theoanu/openDrivePlatform/hardware/lowVoltageDrive/lowVoltageDrive.sch

## KiCad design hardware/lowVoltageDrive/lowVoltageDrive.sch (2013-01-29)

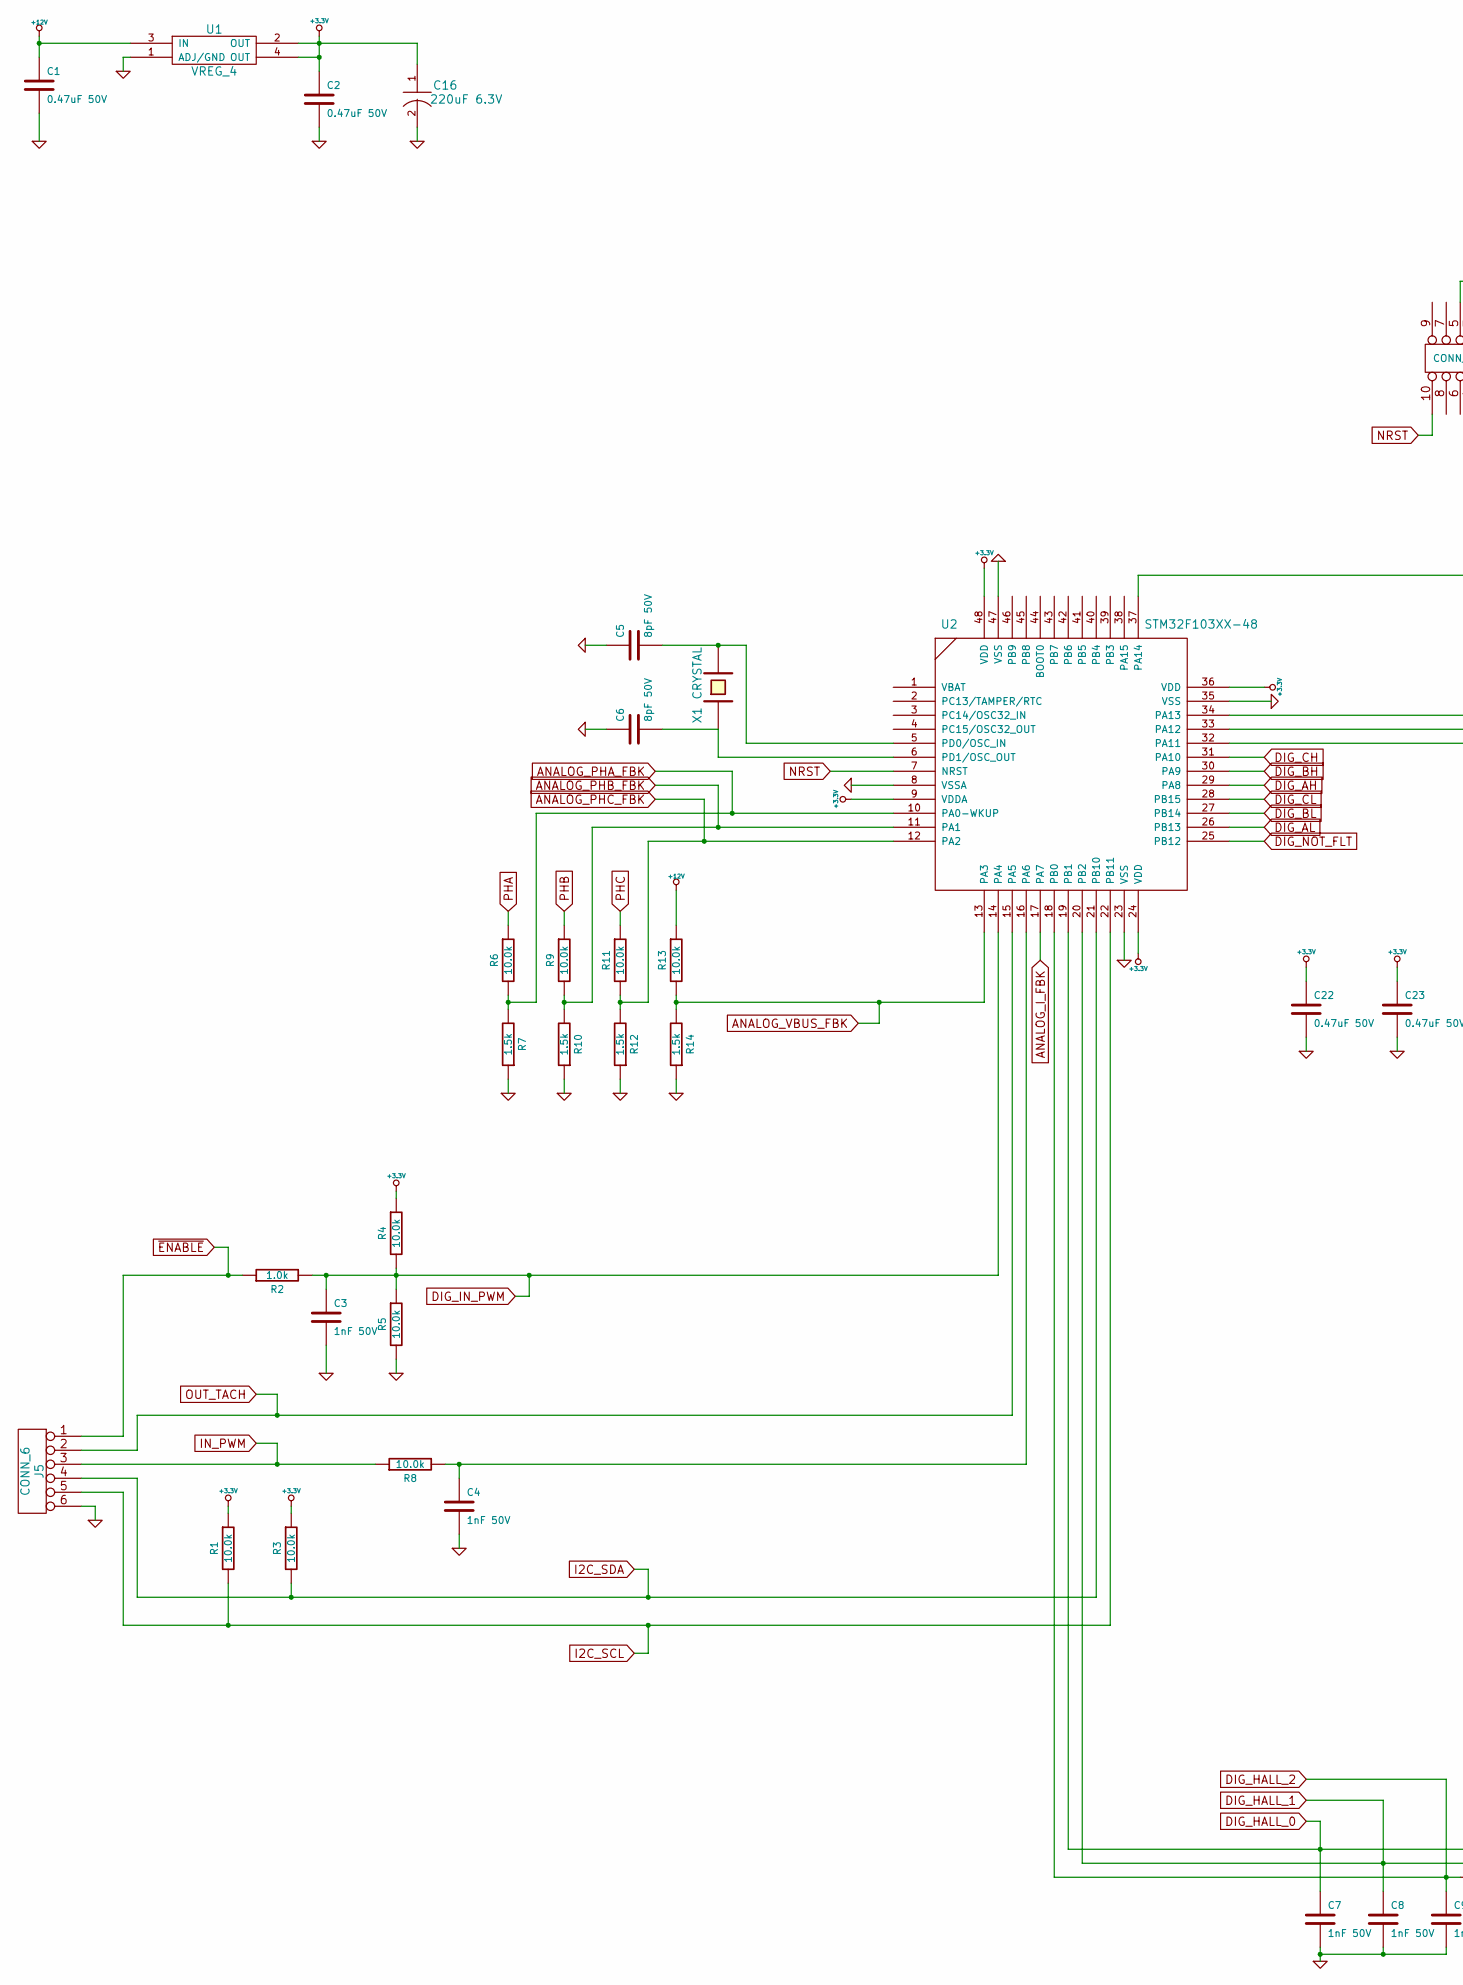
[picture p2: schematic lowVoltageDrive.sch, part in row 1, column 1]

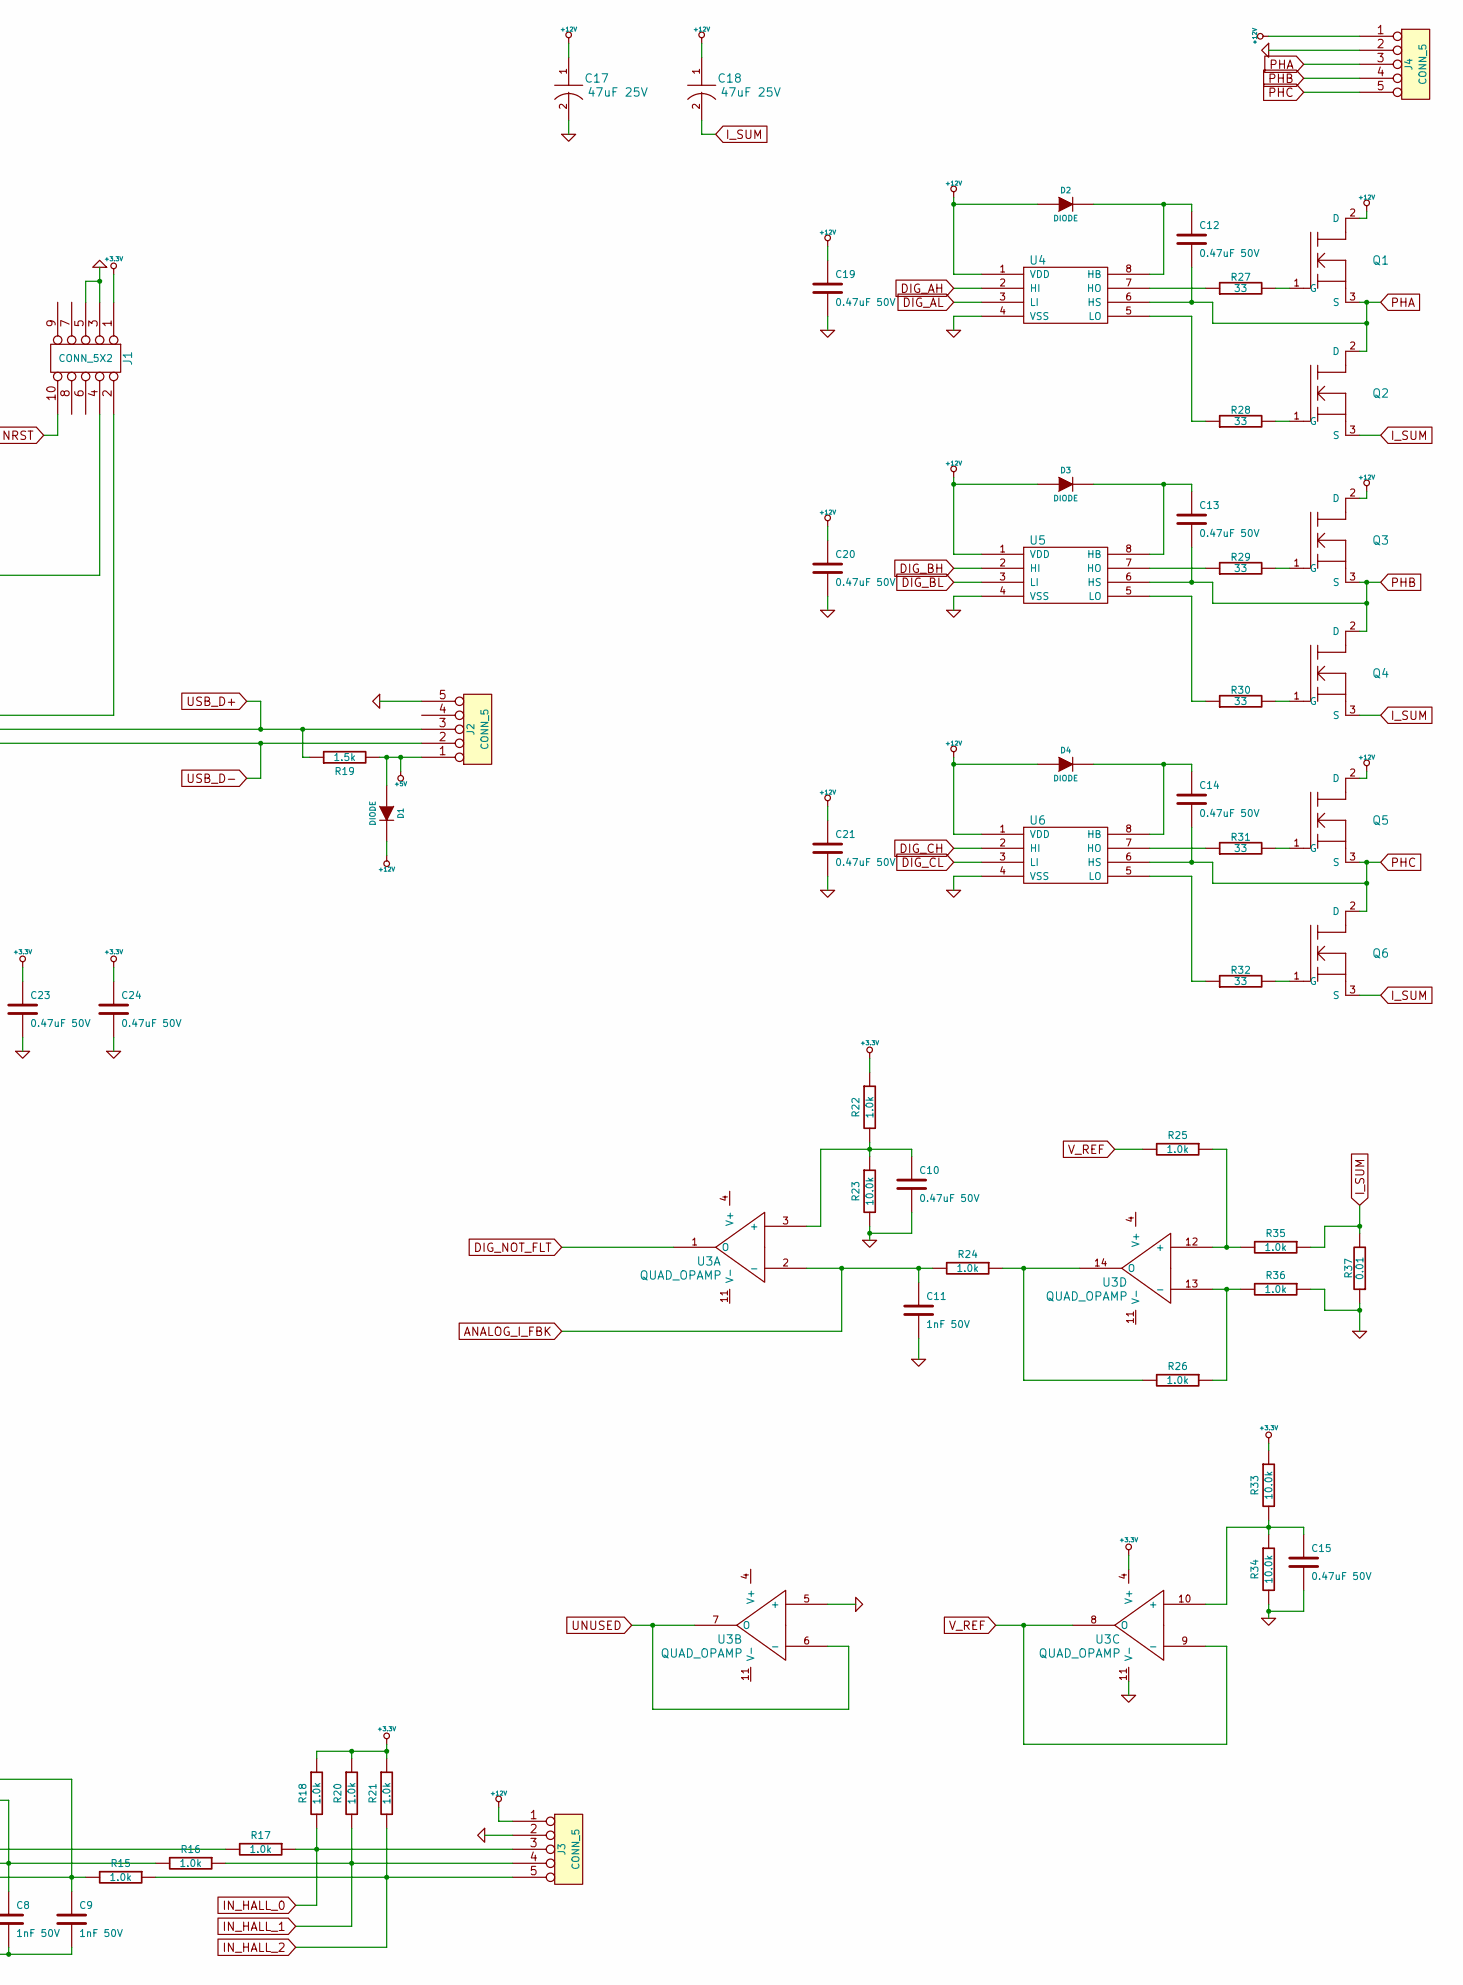
[picture p3: schematic lowVoltageDrive.sch, part in row 1, column 2]

Parts:
C1, C2, C10, C12, C13, C14, C15, C19, C20, C21, C22, C23, C24: 0.47uF 50V; SM0603; Man. Part Number UMK107B7474KA-TR
C3, C4, C7, C8, C9, C11: 1nF 50V; SM0603; Man. Part Number GRM188R71H102KA01D
C5, C6: 8pF 50V; SM0603; Man. Part Number C1608C0G1H080C
C16: 220uF 6.3V; SM_CAP_ALUM_6D3; Man. Part Number EEE-0JA221WP
C17, C18: 47uF 25V; SM_CAP_ALUM_6D3; Man. Part Number EEV476M025A9GAA
D1, D2, D3, D4: DIODE; SOD323; Man. Part Number 1N4148WX-TP
J1: CONN_5X2; CONN10_5X2_0.050
J2: CONN_5; USB_MICRO_AB
J3: CONN_5; CONN5_5-1775444-5; Man. Part Number 5-1775444-5
J4: CONN_5; CONN5_OSTTC050162; Man. Part Number OSTTC050162
J5: CONN_6; CONN6_5-1775444-6; Man. Part Number 5-1775444-6
Q1, Q2, Q3, Q4, Q5, Q6: MOSFET_N_TO220; TO-220-3_tripod; Man. Part Number AOTF240L
R1, R3, R4, R5, R6, R8, R9, R11, R13, R23, R33, R34: 10.0k; SM0603; Man. Part Number RC0603FR-0710KL
R2, R15, R16, R17, R18, R20, R21, R22, R24, R25, R26, R35, R36: 1.0k; SM0603; Man. Part Number RC0603FR-071KL
R7, R10, R12, R14, R19: 1.5k; SM0603; Man. Part Number RC0603FR-071K5L
R27, R28, R29, R30, R31, R32: 33; SM0603; Man. Part Number RC0603JR-0733RL
R37: 0.01; SM2818_POWER; Man. Part Number WSH2818R0100FEA
U1: VREG_4; SOT223; Man. Part Number NCP1117LPST33T3G
U2: STM32F103XX-48; QFP-48; Man. Part Number STM32F103C4T6A
U3: QUAD_OPAMP; SO14N
U4, U5, U6: MOSFET_DRIVER; SO8N; Man. Part Number FAN7842MX
X1: CRYSTAL; CRYSTAL_NDK_NX5032GA; Man. Part Number NX5032GA 8MHZ AT-W

Connections:
+3.3V: C2.1, C16.1, C22.1, C23.1, C24.1, J1.1, R1.1, R3.1, R4.1, R18.1, R20.1, R21.1, R22.1, R33.1, U1.2 (OUT), U1.4 (OUT), U2.9 (VDDA), U2.24 (VDD), U2.36 (VDD), U2.48 (VDD), U3.4 (V+)
+5V: D1.1 (A), J2.1, R19.2
+12V: C1.1, C17.1, C18.1, C19.1, C20.1, C21.1, D1.2 (K), D2.1 (A), D3.1 (A), D4.1 (A), J3.1, J4.1, Q1.2 (D), Q3.2 (D), Q5.2 (D), R13.1, U1.3 (IN), U4.1 (VDD), U5.1 (VDD), U6.1 (VDD)
ANALOG_I_FBK: C11.1, R24.2, U2.17 (PA7), U3.2 (-)
ANALOG_PHA_FBK: R6.2, R7.2, U2.10 (PA0-WKUP)
ANALOG_PHB_FBK: R9.2, R10.2, U2.11 (PA1)
ANALOG_PHC_FBK: R11.2, R12.2, U2.12 (PA2)
ANALOG_VBUS_FBK: R13.2, R14.2, U2.13 (PA3)
DIG_AH: U2.29 (PA8), U4.2 (HI)
DIG_AL: U2.26 (PB13), U4.3 (LI)
DIG_BH: U2.30 (PA9), U5.2 (HI)
DIG_BL: U2.27 (PB14), U5.3 (LI)
DIG_CH: U2.31 (PA10), U6.2 (HI)
DIG_CL: U2.28 (PB15), U6.3 (LI)
DIG_HALL_0: C7.1, R17.2, U2.19 (PB1)
DIG_HALL_1: C8.1, R16.2, U2.20 (PB2)
DIG_HALL_2: C9.1, R15.2, U2.18 (PB0)
DIG_IN_PWM: C3.1, R2.2, R4.2, R5.1, U2.14 (PA4)
DIG_NOT_FLT: U2.25 (PB12), U3.1 (O)
GND: C1.2, C2.2, C3.2, C4.2, C5.1, C6.1, C7.2, C8.2, C9.2, C10.2, C11.2, C15.2, C16.2, C17.2, C19.2, C20.2, C21.2, C22.2, C23.2, C24.2, J1.3, J1.5, J2.5, J3.2, J4.2, J5.6, R5.2, R7.1, R10.1, R12.1, R14.1, R23.2, R34.2, R36.1, R37.1, U1.1 (ADJ/GND), U2.8 (VSSA), U2.23 (VSS), U2.35 (VSS), U2.47 (VSS), U3.5 (+), U3.11 (V-), U4.4 (VSS), U5.4 (VSS), U6.4 (VSS)
I2C_SCL: J5.5, R1.2, U2.22 (PB11)
I2C_SDA: J5.4, R3.2, U2.21 (PB10)
IN_HALL_0: J3.3, R17.1, R18.2
IN_HALL_1: J3.4, R16.1, R20.2
IN_HALL_2: J3.5, R15.1, R21.2
IN_PWM: J5.3, R8.1
I_SUM: C18.2, Q2.3 (S), Q4.3 (S), Q6.3 (S), R35.1, R37.2
NRST: J1.10, U2.7 (NRST)
unnamed: C4.1, R8.2, U2.16 (PA6)
unnamed: C5.2, U2.5 (PD0/OSC_IN), X1.2
unnamed: C6.2, U2.6 (PD1/OSC_OUT), X1.1
unnamed: C10.1, R22.2, R23.1, U3.3 (+)
unnamed: C12.1, D2.2 (K), U4.8 (HB)
unnamed: C13.1, D3.2 (K), U5.8 (HB)
unnamed: C14.1, D4.2 (K), U6.8 (HB)
unnamed: C15.1, R33.2, R34.1, U3.10 (+)
unnamed: J1.2, U2.34 (PA13)
unnamed: J1.4, U2.37 (PA14)
unnamed: Q1.1 (G), R27.2
unnamed: Q2.1 (G), R28.2
unnamed: Q3.1 (G), R29.2
unnamed: Q4.1 (G), R30.2
unnamed: Q5.1 (G), R31.2
unnamed: Q6.1 (G), R32.2
unnamed: R24.1, R26.2, U3.14 (O)
unnamed: R25.1, R35.2, U3.12 (+)
unnamed: R26.1, R36.2, U3.13 (-)
unnamed: R27.1, U4.7 (HO)
unnamed: R28.1, U4.5 (LO)
unnamed: R29.1, U5.7 (HO)
unnamed: R30.1, U5.5 (LO)
unnamed: R31.1, U6.7 (HO)
unnamed: R32.1, U6.5 (LO)
OUT_TACH: J5.2, U2.15 (PA5)
PHA: C12.2, J4.3, Q1.3 (S), Q2.2 (D), R6.1, U4.6 (HS)
PHB: C13.2, J4.4, Q3.3 (S), Q4.2 (D), R9.1, U5.6 (HS)
PHC: C14.2, J4.5, Q5.3 (S), Q6.2 (D), R11.1, U6.6 (HS)
UNUSED: U3.6 (-), U3.7 (O)
USB_D+: J2.3, R19.1, U2.33 (PA12)
USB_D-: J2.2, U2.32 (PA11)
V_REF: R25.2, U3.8 (O), U3.9 (-)
~ENABLE: J5.1, R2.1
